ReiniervdL/Vinduino/Vinduino-Imp-GW-PCB/DSC03003.jpg

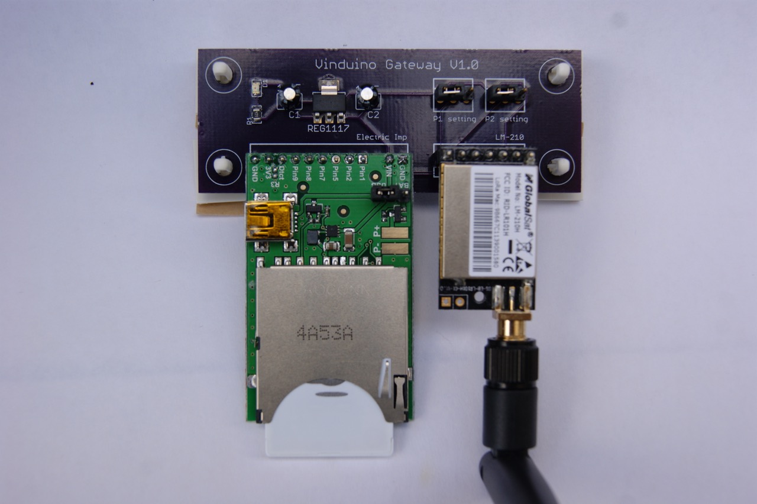
Vinduino-Imp-GW-PCB/DSC03003.jpg
