ReiniervdL/Vinduino/Vinduino-R3/DSC02996.jpg

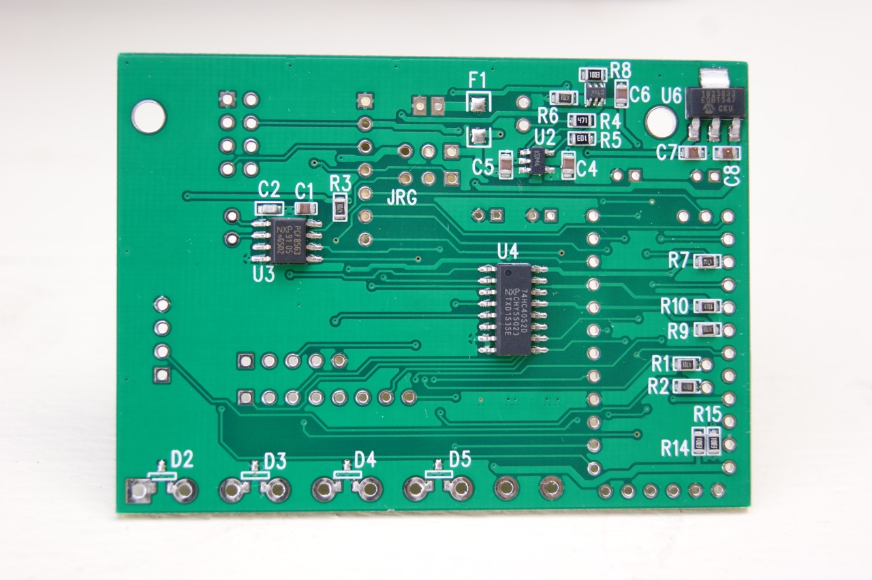
Vinduino-R3/DSC02996.jpg
