ReiniervdL/Vinduino/Vinduino-R3/image001.jpg

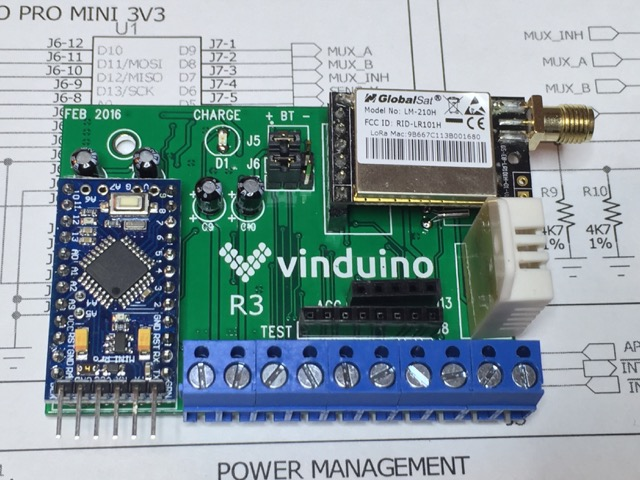
Vinduino-R3/image001.jpg
